codead/STM32-Audio-Hifi/Software/STM32_Audio_v1.1/Drivers/LCD/ST7789/Draw.c

/*
 * Draw.c
 *
 *  Created on: Dec 25, 2022
 *      Author: Duc Huy Le
 */
#include "Draw.h"
#include "ST7789.h"
#include "stdio.h"
#include <string.h>
#include <math.h>
#include <stdbool.h>
#include <string.h>
#include "Display.h"
#include "Icons.h"
#include "FreeRTOS.h"
#include "task.h"
#include "cmsis_os.h"
#include "Play_wav.h"
extern osSemaphoreId binSemaphoreDisplayHandle;
#define PI 3.14
extern AUDIO Audio;
extern uint8_t BatteryStatus;
//extern char Audio.PlayList[255][50];
//extern uint16_t Audio.MaxSong;    //Number of music.
//extern uint16_t Audio.CurrentSong;
extern DISPLAY Display;
extern uint16_t DisplayBuff[];
extern uint32_t volatile volumeSet;
extern __SETTING Setting;
extern uint8_t SCREEN_MUSIC_MAX_LIST;
const PIXEL CircleProgressPixel[] = {
    {0x78, 0x2C},{0x78, 0x2B},{0x78, 0x2A},{0x78, 0x29},{0x78, 0x28},{0x78, 0x27},{0x78, 0x26},{0x78, 0x25},{0x78, 0x24},{0x78, 0x23},{0x78, 0x22},{0x78, 0x21},{0x78, 0x20},{0x78, 0x1F},{0x78, 0x1E},{0x79, 0x2C},{0x79, 0x2B},{0x79, 0x2A},{0x79, 0x29},{0x79, 0x28},
    {0x79, 0x27},{0x79, 0x26},{0x79, 0x25},{0x79, 0x24},{0x79, 0x23},{0x79, 0x22},{0x79, 0x21},{0x79, 0x20},{0x79, 0x1F},{0x79, 0x1E},{0x7A, 0x2C},{0x7A, 0x2B},{0x7A, 0x2A},{0x7A, 0x29},{0x7A, 0x28},{0x7A, 0x27},{0x7A, 0x26},{0x7A, 0x25},{0x7A, 0x24},{0x7A, 0x23},{0x7A, 0x22},{0x7A, 0x21},{0x7A, 0x20},{0x7A, 0x1F},{0x7A, 0x1E},{0x7B, 0x2C},{0x7B, 0x2B},{0x7B, 0x2A},{0x7B, 0x29},{0x7B, 0x28},{0x7B, 0x27},{0x7B, 0x26},{0x7B, 0x25},{0x7B, 0x24},{0x7B, 0x23},{0x7B, 0x22},{0x7B, 0x21},{0x7B, 0x20},{0x7B, 0x1F},{0x7B, 0x1E},{0x7C, 0x2C},{0x7C, 0x2B},{0x7C, 0x2A},{0x7C, 0x29},{0x7C, 0x28},{0x7C, 0x27},{0x7C, 0x26},{0x7C, 0x25},{0x7C, 0x24},{0x7C, 0x23},{0x7C, 0x22},{0x7C, 0x21},{0x7C, 0x20},{0x7C, 0x1F},{0x7C, 0x1E},{0x7D, 0x2C},{0x7D, 0x2B},{0x7D, 0x2A},{0x7D, 0x29},{0x7D, 0x28},{0x7D, 0x27},{0x7D, 0x26},{0x7D, 0x25},{0x7D, 0x24},{0x7D, 0x23},{0x7D, 0x22},{0x7D, 0x21},{0x7D, 0x20},{0x7D, 0x1F},{0x7D, 0x1E},{0x7E, 0x2C},{0x7E, 0x2B},{0x7E, 0x2A},{0x7E, 0x29},{0x7E, 0x28},{0x7E, 0x27},{0x7E, 0x26},{0x7E, 0x25},{0x7E, 0x24},{0x7E, 0x23},{0x7E, 0x22},{0x7E, 0x21},{0x7E, 0x20},{0x7E, 0x1F},{0x7E, 0x1E},{0x7F, 0x2C},{0x7F, 0x2B},{0x7F, 0x2A},{0x7F, 0x29},{0x7F, 0x28},{0x7F, 0x27},{0x7F, 0x26},{0x7F, 0x25},{0x7F, 0x24},{0x7F, 0x23},{0x7F, 0x22},{0x7F, 0x21},{0x7F, 0x20},{0x7F, 0x1F},{0x7F, 0x1E},{0x80, 0x2D},{0x80, 0x2C},{0x80, 0x2B},{0x80, 0x2A},{0x80, 0x29},{0x80, 0x28},{0x80, 0x27},{0x80, 0x26},{0x80, 0x25},{0x80, 0x24},{0x80, 0x23},{0x80, 0x22},{0x80, 0x21},{0x80, 0x20},{0x80, 0x1F},{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

};
void Draw_CircleProgress(uint16_t x0, uint16_t y0, uint16_t r, uint16_t alpha)
{

  uint16_t x, y;
  uint16_t alpha_split[4] = {0};
  uint8_t quarter;
  uint8_t curent_quarter;
  static uint8_t previous_quarter = 0;
  if(alpha > 360)
  {
    alpha_split[0] = 90;
    alpha_split[1] = 90;
    alpha_split[2] = 90;
    alpha_split[3] = 90;
    quarter = 4;
  }
  else if(alpha > 270)
  {
    alpha_split[0] = 90;
    alpha_split[1] = 90;
    alpha_split[2] = 90;
    alpha_split[3] = alpha - 270;
    quarter = 4;
  }
  else if(alpha > 180)
  {
    alpha_split[0] = 90;
    alpha_split[1] = 90;
    alpha_split[2] = alpha - 180;
    quarter = 3;
  }
  else if(alpha > 90)
  {
    alpha_split[0] = 90;
    alpha_split[1] = alpha - 90;
    quarter = 2;
  }
  else
  {
    alpha_split[0] = alpha;
    quarter = 1;
  }
  ST7789_DrawPixel( x0, y0, BLACK);
  for(curent_quarter = previous_quarter; curent_quarter < quarter; curent_quarter++)
  {
    for(x = 0; x <= r; x++)
    {
      for(y = 0; y <= r; y++)
      {
        if((x * x + y * y) < (r + 1) * r)
        {
//            if((x * x + y * y) >= (r - 10 + 1) * (r - 10))
//            {
            if((curent_quarter == 0) && (y != 0) && (((double)x / (double)y) <= tan((double)alpha_split[0] * 2 * PI / 360)))
            {
              ST7789_DrawPixel(x0 + x, y0 - y, RED);
            }
            else if((curent_quarter == 1) && (x != 0) && (((double)y / (double)x) <= tan((double)alpha_split[1] * 2 * PI / 360)))
            {
              ST7789_DrawPixel(x0 + x, y0 + y, RED);
            }
            else if((curent_quarter == 2) && (y != 0) && (((double)x / (double)y) <= tan((double)alpha_split[2] * 2 * PI / 360)))
            {
              ST7789_DrawPixel(x0 - x, y0 + y, RED);
            }
            else if((curent_quarter == 3) && (x != 0) && (((double)y / (double)x) <= tan((double)alpha_split[3] * 2 * PI / 360)))
            {
              ST7789_DrawPixel(x0 - x, y0 - y, RED);
            }

  //          else if(y == 0 && alpha_split[0] == 90)
  //          {
  //            ST7789_DrawPixel( x0 + x, y0 - y, RED);
  //          }
//          }
        }
        else
        {

          break;
        }
      }
    }
  }

  previous_quarter = curent_quarter - 1;
  //printf("previous_quarter = %d, x = %d, y = %d\n", previous_quarter, previous_x, previous_y);
}
void Draw_Pixel(uint16_t x, uint16_t y, uint16_t color)
{

}
void Draw_LineCircleProgress(uint16_t x0, uint16_t y0, uint16_t r, uint16_t width, uint8_t percent, uint16_t color)
{
  uint16_t x, y;
  double alpha;
  uint16_t alpha_split[4] = {0};
  uint8_t quarter;
  uint8_t curent_quarter;
  static uint8_t previous_quarter = 0;
  //convert percent to deg
  alpha = (double)percent * 360 / 100;
//  uint16_t counter = 0;
  if(alpha > 360)
  {
    alpha_split[0] = 90;
    alpha_split[1] = 90;
    alpha_split[2] = 90;
    alpha_split[3] = 90;
    quarter = 4;
  }
  else if(alpha > 270)
  {
    alpha_split[0] = 90;
    alpha_split[1] = 90;
    alpha_split[2] = 90;
    alpha_split[3] = alpha - 270;
    quarter = 4;
  }
  else if(alpha > 180)
  {
    alpha_split[0] = 90;
    alpha_split[1] = 90;
    alpha_split[2] = alpha - 180;
    quarter = 3;
  }
  else if(alpha > 90)
  {
    alpha_split[0] = 90;
    alpha_split[1] = alpha - 90;
    quarter = 2;
  }
  else
  {
    alpha_split[0] = alpha;
    quarter = 1;
  }
  for(curent_quarter = previous_quarter; curent_quarter < quarter; curent_quarter++)
  {
    for(x = 0; x <= r; x++)
    {
      for(y = 0; y <= r; y++)
      {
        if((x * x + y * y) < (r + 1) * r)
        {
          if((x * x + y * y) >= (r - width + 1) * (r - width))
          {
            if((curent_quarter == 0) && (y != 0) && (((double)x / (double)y) <= tan((double)alpha_split[0] * 2 * PI / 360)))
            {
              ST7789_DrawPixel(x0 + x, y0 - y, color);
//              printf("{0x%X, 0x%X},",x0 + x, y0 - y);
//              counter++;
//              if(counter == 20)
//              {
//                printf("\n");
//              }
            }
            else if((curent_quarter == 1) && (x != 0) && (((double)y / (double)x) <= tan((double)alpha_split[1] * 2 * PI / 360)))
            {
              ST7789_DrawPixel(x0 + x, y0 + y, color);
//              printf("{0x%X, 0x%X},",x0 + x, y0 + y);
//              counter++;
//              if(counter == 20)
//              {
//                printf("\n");
//              }
            }
            else if((curent_quarter == 2) && (y != 0) && (((double)x / (double)y) <= tan((double)alpha_split[2] * 2 * PI / 360)))
            {
              ST7789_DrawPixel(x0 - x, y0 + y, color);
//              printf("{0x%X, 0x%X},",x0 - x, y0 + y);
//              counter++;
//              if(counter == 20)
//              {
//                printf("\n");
//              }
            }
            else if((curent_quarter == 3) && (x != 0) && (((double)y / (double)x) <= tan((double)alpha_split[3] * 2 * PI / 360)))
            {
              ST7789_DrawPixel(x0 - x, y0 - y, color);
//              printf("{0x%X, 0x%X},",x0 - x, y0 - y);
//              counter++;
//              if(counter == 20)
//              {
//                printf("\n");
//              }
            }
          }
        }
        else
        {
          break;
        }
      }
    }
  }
//printf("counter = %d\n", counter);
  previous_quarter = curent_quarter - 1;
  //printf("previous_quarter = %d, x = %d, y = %d\n", previous_quarter, previous_x, previous_y);
}
void Draw_CreateLineCircleProgress(uint16_t x0, uint16_t y0, uint16_t r, uint16_t width, uint8_t percent, uint16_t color)
{
  uint16_t x, y;
  double alpha;
  uint16_t alpha_split[4] = {0};
  uint8_t quarter;
  uint8_t curent_quarter;
  uint8_t previous_quarter = 0;
  //convert percent to deg
  alpha = (double)percent * 360 / 100;
//  uint16_t counter = 0;
  if(alpha > 360)
  {
    alpha_split[0] = 90;
    alpha_split[1] = 90;
    alpha_split[2] = 90;
    alpha_split[3] = 90;
    quarter = 4;
  }
  else if(alpha > 270)
  {
    alpha_split[0] = 90;
    alpha_split[1] = 90;
    alpha_split[2] = 90;
    alpha_split[3] = alpha - 270;
    quarter = 4;
  }
  else if(alpha > 180)
  {
    alpha_split[0] = 90;
    alpha_split[1] = 90;
    alpha_split[2] = alpha - 180;
    quarter = 3;
  }
  else if(alpha > 90)
  {
    alpha_split[0] = 90;
    alpha_split[1] = alpha - 90;
    quarter = 2;
  }
  else
  {
    alpha_split[0] = alpha;
    quarter = 1;
  }
  for(curent_quarter = previous_quarter; curent_quarter < quarter; curent_quarter++)
  {
    for(x = 0; x <= r; x++)
    {
      for(y = 0; y <= r; y++)
      {
        if((x * x + y * y) < (r + 1) * r)
        {
          if((x * x + y * y) >= (r - width + 1) * (r - width))
          {
            if((curent_quarter == 0) && (y != 0) && (((double)x / (double)y) <= tan((double)alpha_split[0] * 2 * PI / 360)))
            {
              ST7789_DrawPixel(x0 + x, y0 - y, color);
            }
            else if((curent_quarter == 1) && (x != 0) && (((double)y / (double)x) <= tan((double)alpha_split[1] * 2 * PI / 360)))
            {
              ST7789_DrawPixel(x0 + x, y0 + y, color);
            }
            else if((curent_quarter == 2) && (y != 0) && (((double)x / (double)y) <= tan((double)alpha_split[2] * 2 * PI / 360)))
            {
              ST7789_DrawPixel(x0 - x, y0 + y, color);
            }
            else if((curent_quarter == 3) && (x != 0) && (((double)y / (double)x) <= tan((double)alpha_split[3] * 2 * PI / 360)))
            {
              ST7789_DrawPixel(x0 - x, y0 - y, color);
            }
          }
        }
        else
        {
          break;
        }
      }
    }
  }
  previous_quarter = curent_quarter - 1;
}
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
