codead/STM32-Audio-Hifi/Software/STM32_Audio_v1.1/Drivers/LCD/ST7789/Icons.c

/*
 * Icons.c
 *
 *  Created on: Feb 11, 2023
 *      Author: Duc Huy Le
 */

#include "Icons.h"

const uint16_t Battery_Full[] =
{
    0xffff, 0x55ad, 0x3084, 0x3084, 0x3084, 0x3084, 0x3084, 0x3084, 0x3084, 0x3084, 0x3084, 0x3084, 0x3084, 0x3084, 0x3084, 0x3084, 0x3084, 0x3084, 0x3084, 0x3084, 0x3084, 0x3084, 0x3084, 0x3084, 0x3084, 0x3084, 0x3084, 0x3084, 0x1ce7, 0xffff, 0xffff, 0xffff,
    0x55ad, 0xb6b5, 0x329f, 0xcd76, 0xcd76, 0xcd76, 0xcd76, 0xcd76, 0xcd76, 0xcd76, 0xcd76, 0xcd76, 0xcd76, 0xcd76, 0xcd76, 0xcd76, 0xcd76, 0xcd76, 0xcd76, 0xcd76, 0xcd76, 0xcd76, 0xcd76, 0xcd76, 0xcd76, 0xcd76, 0xef86, 0x38c7, 0xef7b, 0xdfff, 0xffff, 0xffff,
    0x3084, 0x329f, 0x6646, 0x6646, 0x6646, 0x6646, 0x6646, 0x6646, 0x6646, 0x6646, 0x6646, 0x6646, 0x6646, 0x6646, 0x6646, 0x6646, 0x6646, 0x6646, 0x6646, 0x6646, 0x6646, 0x6646, 0x6646, 0x6646, 0x6646, 0x6646, 0x6646, 0x684e, 0xb6b5, 0x38c6, 0xffff, 0xffff,
    0xef7b, 0xcd76, 0x6646, 0x6646, 0x6646, 0x6646, 0x6646, 0x6646, 0x6646, 0x6646, 0x6646, 0x6646, 0x6646, 0x6646, 0x6646, 0x6646, 0x6646, 0x6646, 0x6646, 0x6646, 0x6646, 0x6646, 0x6646, 0x6646, 0x6646, 0x6646, 0x6646, 0x6646, 0xb8c6, 0x55ad, 0xffff, 0xffff,
    0xef7b, 0xcd76, 0x6646, 0x6646, 0x6646, 0x6646, 0x6646, 0x6646, 0x6646, 0x6646, 0x6646, 0x6646, 0x6646, 0x6646, 0x6646, 0x6646, 0x6646, 0x6646, 0x6646, 0x6646, 0x6646, 0x6646, 0x6646, 0x6646, 0x6646, 0x6646, 0x6646, 0x6646, 0xb8c6, 0x55ad, 0xffff, 0xffff,
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
    0xffff, 0xffff, 0xffff, 0xffff, 0xffff, 0xffff, 0xffff, 0xffff, 0xffff, 0xffff, 0x3fe7, 0xfcbd, 0x9cad, 0x3ec6, 0xdfd6, 0xdfde, 0xbfde, 0x9fde, 0x1ece, 0x3bb5, 0x9bc5, 0x1fef, 0xdfff, 0xffff, 0xffff, 0xffff, 0xffff, 0xffff, 0xffff, 0xffff, 0xffff, 0xffff,
    0xffff, 0xffff, 0xffff, 0xffff, 0xffff, 0xffff, 0xffff, 0xffff, 0xffff, 0xffff, 0xbff7, 0x7dce, 0xbdb5, 0x9ead, 0xbeb5, 0xbdb5, 0x7dbd, 0x5dbd, 0x5dbd, 0x5cbd, 0x3dd6, 0x7ff7, 0xffff, 0xffff, 0xffff, 0xffff, 0xffff, 0xffff, 0xffff, 0xffff, 0xffff, 0xffff,
    0xffff, 0xffff, 0xffff, 0xffff, 0xffff, 0xffff, 0xffff, 0xffff, 0xffff, 0xffff, 0xffff, 0xffde, 0x1fc6, 0x9fb5, 0x7ead, 0x7ead, 0x5ebd, 0x3dbd, 0x3ebd, 0xbfcd, 0xdfe6, 0xdfff, 0xffff, 0xffff, 0xffff, 0xffff, 0xffff, 0xffff, 0xffff, 0xffff, 0xffff, 0xffff

};
