codead/STM32-Audio-Hifi/Software/STM32_Audio_v1.1/Drivers/IO_Expand/Button_Led.h

/*
 * Button_Led.h
 *
 *  Created on: Jul 25, 2022
 *      Author: Duc Huy Le
 */

#ifndef IO_EXPAND_BUTTON_LED_H_
#define IO_EXPAND_BUTTON_LED_H_

#define BTN_LEFT          2
#define BTN_DOWN          3
#define LED_DOWN          4
#define BTN_RIGHT         5
#define LED_LEFT          6
#define LED_RIGHT         7
#define BTN_CENTRE        8
#define BTN_UP            9
#define LED_CENTRE        12
#define LED_UP            13

#endif /* IO_EXPAND_BUTTON_LED_H_ */
