codead/STM32-Audio-Hifi/Software/STM32_Audio_v1.1/Drivers/LCD/ST7789/Icons.h

/*
 * Icons.h
 *
 *  Created on: Feb 11, 2023
 *      Author: Duc Huy Le
 */

#ifndef LCD_ST7789_ICONS_H_
#define LCD_ST7789_ICONS_H_
#include "stdint.h"
extern const uint16_t Battery_Charge[];
extern const uint16_t Battery_Full[];
extern const uint16_t Battery_Prohibiton[];
extern const uint16_t Play_List_Icon[];
extern const uint16_t Volume_Icon[];
extern const uint16_t Volume_Progress_Icon[];
extern const uint16_t Toggle_Button_On_Data[];
extern const uint16_t Toggle_Button_Off_Data[];
extern const uint16_t Setting_Icon[];
#endif /* LCD_ST7789_ICONS_H_ */
